farvardin/garvuino/atmega8/amstrad_6128_audio_out.png

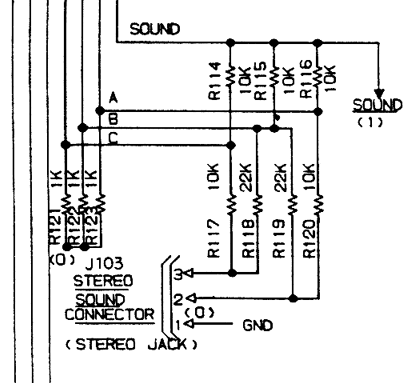
atmega8/amstrad_6128_audio_out.png
