farvardin/garvuino/tools/wave_generator/images/watermelon-duck-outline.png

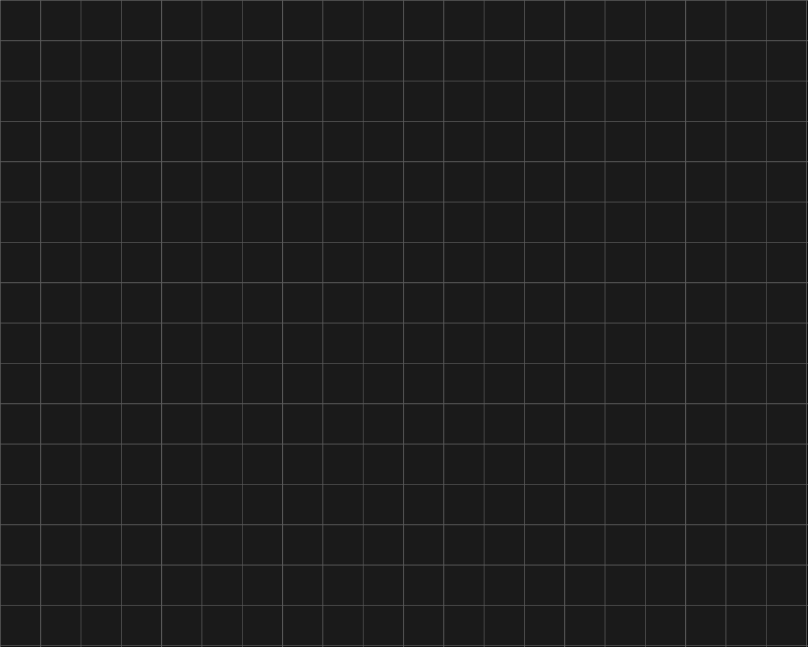
tools/wave_generator/images/watermelon-duck-outline.png
