farvardin/garvuino/arduino_sketches/others/playtune/miditone/garvalf_fugue01.ino

#include <Playtune.h>
// Playtune bytestream for file "garvalf_fugue01.mid" created by MIDITONES V2.00 on Mon Jun 22 09:18:14 2020
// command line: ./miditones -v -i -pt -d -t=4 garvalf_fugue01 
const unsigned char PROGMEM score [] = {
'P','t', 6, 0xE0, 0x00,  4, // (Playtune file header)
0xC0,40, 0x90,64,80, 0,177, 0x80, 0,1, 0x90,69,80, 0,177, 0x80, 0,2, 0x90,72,80, 0,177, 0x80, 0,1, 
0x90,71,80, 0,177, 0x80, 0,2, 0x90,68,80, 0,177, 0x80, 0,1, 0x90,71,80, 0,177, 0x80, 0,2, 0x90,69,80, 
0,177, 0x80, 0,1, 0x90,71,80, 0,178, 0x80, 0,1, 0x90,72,80, 0,177, 0x80, 0,2, 0x90,74,80, 0,177, 
0x80, 0,1, 0x90,76,80, 0,177, 0x80, 0,2, 0x90,74,80, 0,177, 0x80, 0,1, 0x90,69,80, 0,177, 0x80, 0,2, 
0x90,72,80, 0,177, 0x80, 0,1, 0x90,71,80, 1,100, 0x80, 0,2, 0x90,72,80, 0,177, 0x80, 0,1, 0x90,74,80, 
0,177, 0x80, 0,2, 0x90,76,80, 0,177, 0x80, 0,1, 0x90,74,80, 0,177, 0x80, 0,2, 0x90,77,80, 0,177, 
0x80, 0,1, 0x90,76,80, 0,178, 0x80, 0,1, 0x90,74,80, 1,100, 0x80, 0,1, 0x90,72,80, 0,177, 0x80, 0,2, 
0x90,74,80, 0,177, 0x80, 0,1, 0x90,76,80, 0,177, 0x80, 0,2, 0x90,74,80, 0,177, 0x80, 0,1, 0x90,72,80, 
0,178, 0x80, 0,1, 0x90,71,80, 0,177, 0x80, 0,2, 0x90,69,80, 1,99, 0x80, 0,2, 0x90,72,80, 0,177, 
0x80, 0,1, 0x90,76,80, 0,177, 0x80, 0,2, 0x90,79,80, 0,177, 0x80, 0,1, 0x90,77,80, 0,178, 0x80, 0,1, 
0x90,76,80, 0,177, 0x80, 0,2, 0x90,74,80, 0,177, 0x80, 0,1, 0x90,72,80, 1,100, 0x80, 0,1, 0xC0,41, 
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
Playtune pt; 
 void setup() {
  pt.tune_initchan (10); 
  pt.tune_initchan (11);
  pt.tune_initchan (12);
}

 void loop () {
  pt.tune_playscore((byte *) score);  /* start playing */
  while (pt.tune_playing) ;   /* wait here until playing stops */
}
