farvardin/garvuino/arduino_sketches/mozzi/mozzi_MIDI_portamento_POT/mozzi_MIDI_portamento_POT.ino

/* 
 *  Mozzi + Midi + Control portamento strength with Pot 1 in A0  
 * 
 *  version for Garvuino https://github.com/farvardin/garvuino
 *  Works with Arduino IDE 1.8.3
 *  
 *  (it might crackle and produce hiss and noise if the Pot value is too high)
 */


/*  Example of a sound being triggered by MIDI input, with portamento.
  
    Demonstrates playing notes with Mozzi in response to MIDI input.
    Also demonstrates Portamento(), a traditional portamento with a 
    duration which can be set.
  
    Uses Arduino MIDI library v4.2 
    (https://github.com/FortySevenEffects/arduino_midi_library/releases/tag/4.2)
    
    Circuit: 
      MIDI input circuit as per http://arduino.cc/en/Tutorial/Midi
      (midi has to be disconnected from rx for sketch to upload)
      Audio output on digital pin 9 on a Uno or similar.
      
    Mozzi help/discussion/announcements:
    https://groups.google.com/forum/#!forum/mozzi-users
  
    Tim Barrass 2013, CC by-nc-sa.
*/

#include <MIDI.h>
#include <MozziGuts.h>
#include <Oscil.h> // oscillator template
#include <Line.h> // for envelope
#include <tables/sin2048_int8.h> // sine table for oscillator
#include <mozzi_midi.h>
#include <ADSR.h>
#include <mozzi_fixmath.h>
#include <Portamento.h>

MIDI_CREATE_DEFAULT_INSTANCE();

// use #define for CONTROL_RATE, not a constant
#define CONTROL_RATE 128 // powers of 2 please

// audio sinewave oscillator
Oscil <SIN2048_NUM_CELLS, AUDIO_RATE> aSin(SIN2048_DATA);

// envelope generator
ADSR <CONTROL_RATE, AUDIO_RATE> envelope;

Portamento <CONTROL_RATE>aPortamento;

#define LED 8 

const int KNOB_PIN_1 = 0; // set the input for the knob to analog pin 0
int knob_value_1 = 5;

void HandleNoteOn(byte channel, byte note, byte velocity) {
  aPortamento.start(note);
  envelope.noteOn();
  digitalWrite(LED,HIGH);
}



void HandleNoteOff(byte channel, byte note, byte velocity) { 
  envelope.noteOff();
  digitalWrite(LED,LOW);
}



void setup() {
  pinMode(LED, OUTPUT);

  // Initiate MIDI communications, listen to all channels
  MIDI.begin(MIDI_CHANNEL_OMNI);    

  // Connect the HandleNoteOn function to the library, so it is called upon reception of a NoteOn.
  MIDI.setHandleNoteOn(HandleNoteOn);  // Put only the name of the function
  MIDI.setHandleNoteOff(HandleNoteOff);  // Put only the name of the function

  envelope.setADLevels(255,64);
  envelope.setTimes(50,200,10000,300); // 10000 is so the note will sustain 10 seconds unless a noteOff comes

  //aPortamento.setTime(300u);

  startMozzi(CONTROL_RATE); 
  //Serial.begin(115200);
}


void updateControl(){
  MIDI.read();
  envelope.update();
  int knob_value_1 = analogRead(KNOB_PIN_1); // value is 0-1023
  int knob_value_remap = map(knob_value_1,0,1023, 1, 500);
  //int knob_value_constrained constrain(knob_value_1,10,255);
  aPortamento.setTime(knob_value_remap);
  aSin.setFreq_Q16n16(aPortamento.next());
 //Serial.print("input = ");
 // Serial.println((int)input);
 //  Serial.print("knob = ");
  //Serial.println((int)KNOB_PIN_1);
}


int updateAudio(){
  return (int) (envelope.next() * aSin.next())>>8;
}


void loop() {
  audioHook(); // required here
} 
