farvardin/garvuino/arduino_sketches/others/the_synth_midi/WTellOver/SongDat3.h

//*************************************************
//10740 bytes 0 based.
//Adapted from Tandy Color Computer by Rich Cook in March 2016
//  THE WILLIAM TELLOVERTURE
//  BY GARRY AND LINDA HOWARD
//  8931 COMANCHE ROAD LONGMONT, COLORADO 80501
//  COPYRIGHT 1982
//
//Modified 255 for no note change
//*************************************************
//
// time (0-127), note1, note2, note3, note4
//
#include <avr/pgmspace.h>
const PROGMEM char mynotes[] = {
32, 67, 59, 50, 43, 
8, 69, 255, 255, 255, 
8, 62, 255, 255, 255, 
8, 67, 255, 255, 255, 
8, 71, 255, 255, 255, 
8, 62, 255, 255, 255, 
32, 67, 255, 255, 255, 
8, 69, 255, 255, 255, 
8, 62, 255, 255, 255, 
8, 67, 255, 255, 255, 
8, 71, 255, 255, 255, 
8, 62, 255, 255, 255, 
32, 67, 255, 255, 255, 
8, 71, 255, 255, 255, 
8, 76, 255, 255, 255, 
8, 74, 255, 255, 255, 
8, 62, 255, 255, 255, 
8, 71, 255, 255, 255, 
68, 69, 50, 54, 57, 
2, 68, 255, 255, 255, 
2, 69, 255, 255, 255, 
24, 74, 255, 255, 255, 
48, 0, 0, 0, 0, 
32, 67, 59, 55, 50, 
8, 69, 255, 255, 255, 
8, 62, 255, 255, 255, 
8, 67, 255, 255, 255, 
8, 71, 255, 255, 255, 
8, 62, 255, 255, 255, 
32, 67, 255, 255, 255, 
8, 69, 255, 255, 255, 
8, 62, 255, 255, 255, 
8, 67, 255, 255, 255, 
8, 71, 255, 255, 255, 
8, 62, 255, 255, 255, 
32, 67, 255, 255, 255, 
8, 71, 255, 255, 255, 
8, 76, 255, 255, 255, 
8, 74, 255, 255, 255, 
8, 62, 255, 255, 255, 
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

};
