farvardin/garvuino/arduino_sketches/others/playtune/playtune_nano/bach01.h

// Playtune bytestream for file "bach_bwv798.mid" created by MIDITONES V1.1 on Sun Feb 27 12:45:00 2011
const byte PROGMEM score [] = {
  // Sinfonia No.12 in A major BWV.798 J.S.Bach
  // Conductor Track
  7,208, 0x90,0x45, 0x91,0x39, 1,77, 0x80, 0x81, 0x90,0x44, 0,166, 0x80, 0x90,0x45, 0,166, 0x80, 0x90,0x47, 
  0x91,0x38, 1,77, 0x80, 0x81, 0x90,0x45, 0,166, 0x80, 0x90,0x44, 0,166, 0x80, 0x90,0x45, 0x91,0x36, 1,77, 
  0x81, 1,77, 0x91,0x31, 0,166, 0x80, 0x90,0x47, 0,166, 0x80, 0x81, 0x90,0x44, 0,166, 0x80, 0x90,0x45, 
  0,166, 0x80, 0x90,0x47, 0x91,0x32, 0,166, 0x80, 0x90,0x40, 0,166, 0x80, 0x81, 0x90,0x49, 0,166, 0x80, 
  0x90,0x40, 0,166, 0x80, 0x90,0x4A, 0x91,0x34, 0,166, 0x80, 0x90,0x40, 0,166, 0x80, 0x81, 0x90,0x4C, 1,77, 
  0x80, 0x90,0x49, 0x91,0x2D, 0,166, 0x80, 0x90,0x47, 0,166, 0x80, 0x81, 0x90,0x45, 0x91,0x39, 0,166, 0x80, 
  0x90,0x47, 0,166, 0x80, 0x81, 0x90,0x49, 0x91,0x38, 0,166, 0x80, 0x90,0x4B, 0,166, 0x80, 0x81, 0x90,0x4C, 
  0x91,0x36, 0,166, 0x80, 0x90,0x4E, 0,166, 0x80, 0x81, 0x90,0x50, 0x91,0x34, 0x92,0x40, 0,166, 0x80, 0x90,0x51, 
  0,166, 0x80, 0x81, 0x82, 0x90,0x53, 0x91,0x3F, 0,166, 0x81, 0x91,0x40, 0,166, 0x81, 0x91,0x3F, 0x92,0x42, 
  0,166, 0x80, 0x90,0x51, 0,166, 0x80, 0x81, 0x82, 0x90,0x50, 0x91,0x40, 0,166, 0x80, 0x81, 0x90,0x4E, 0x91,0x3F, 
  0,166, 0x80, 0x81, 0x90,0x4C, 0x91,0x3D, 0x92,0x40, 0,166, 0x80, 0x90,0x4B, 0,166, 0x80, 0x81, 0x90,0x49, 
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
  0x91,0x3F, 0x92,0x3B, 1,77, 0x80, 0x81, 0x82, 0x90,0x50, 0x91,0x34, 0x92,0x40, 0,166, 0x80, 0x90,0x51, 0,166, 
  0x80, 0x90,0x53, 0,166, 0x80, 0x90,0x51, 0,166, 0x80, 0x81, 0x82, 0x90,0x50, 0,166, 0x80, 0x90,0x4E, 0x91,0x39, 
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
// This score contains 3203 bytes, and 3 tone generators are used.
