farvardin/garvuino/arduino_sketches/others/vra8-n-mono_7/DigitalSynthVRA8N/filter-table.h

#pragma once

const uint8_t g_filter_lpf_table_0[] PROGMEM = {
  0x18, 0x00, 0x20, 0x87, 0x18, 0x00, 0x20, 0x87, 0x18, 0x00, 0x20, 0x87, 0x18, 0x00, 0x20, 0x87,
  0x18, 0x00, 0x20, 0x87, 0x19, 0x00, 0x55, 0x87, 0x1a, 0x00, 0x8c, 0x87, 0x1c, 0x00, 0xc5, 0x87,
  0x1e, 0x00, 0xff, 0x87, 0x1f, 0x00, 0x3b, 0x88, 0x21, 0x00, 0x78, 0x88, 0x23, 0x00, 0xb8, 0x88,
  0x25, 0x00, 0xf9, 0x88, 0x27, 0x00, 0x3c, 0x89, 0x2a, 0x00, 0x81, 0x89, 0x2c, 0x00, 0xc8, 0x89,
  0x2f, 0x00, 0x11, 0x8a, 0x31, 0x00, 0x5d, 0x8a, 0x34, 0x00, 0xaa, 0x8a, 0x37, 0x00, 0xfa, 0x8a,
  0x3a, 0x00, 0x4c, 0x8b, 0x3e, 0x00, 0xa0, 0x8b, 0x41, 0x00, 0xf7, 0x8b, 0x45, 0x00, 0x50, 0x8c,
  0x49, 0x00, 0xac, 0x8c, 0x4d, 0x00, 0x0b, 0x8d, 0x51, 0x00, 0x6c, 0x8d, 0x56, 0x00, 0xd0, 0x8d,
  0x5b, 0x00, 0x37, 0x8e, 0x60, 0x00, 0xa1, 0x8e, 0x65, 0x00, 0x0e, 0x8f, 0x6b, 0x00, 0x7e, 0x8f,
  0x71, 0x00, 0xf1, 0x8f, 0x78, 0x00, 0x68, 0x90, 0x7e, 0x00, 0xe2, 0x90, 0x85, 0x00, 0x5f, 0x91,
  0x8d, 0x00, 0xe1, 0x91, 0x95, 0x00, 0x65, 0x92, 0x9d, 0x00, 0xee, 0x92, 0xa6, 0x00, 0x7a, 0x93,
  0xaf, 0x00, 0x0b, 0x94, 0xb8, 0x00, 0x9f, 0x94, 0xc3, 0x00, 0x38, 0x95, 0xcd, 0x00, 0xd5, 0x95,
  0xd9, 0x00, 0x76, 0x96, 0xe4, 0x00, 0x1d, 0x97, 0xf1, 0x00, 0xc7, 0x97, 0xfe, 0x00, 0x77, 0x98,
  0x0c, 0x01, 0x2b, 0x99, 0x1a, 0x01, 0xe5, 0x99, 0x2a, 0x01, 0xa3, 0x9a, 0x3a, 0x01, 0x67, 0x9b,
  0x4b, 0x01, 0x30, 0x9c, 0x5c, 0x01, 0xff, 0x9c, 0x6f, 0x01, 0xd4, 0x9d, 0x83, 0x01, 0xaf, 0x9e,
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
};

const uint8_t* g_filter_lpf_tables[] = {
  g_filter_lpf_table_0 , g_filter_lpf_table_1 , g_filter_lpf_table_2 , g_filter_lpf_table_3 ,
  g_filter_lpf_table_4 , g_filter_lpf_table_5 , g_filter_lpf_table_6 , g_filter_lpf_table_7 ,
  g_filter_lpf_table_7 , };
