farvardin/garvuino/arduino_sketches/others/vra8-n-mono_7/DigitalSynthVRA8N/osc-table.h

#pragma once

const __uint24 g_osc_freq_table[] = {
  0x000893, 0x000915, 0x00099F, 0x000A31, 0x000ACD, 0x000B71,
  0x000C1F, 0x000CD9, 0x000D9B, 0x000E6B, 0x000F47, 0x00102F,
  0x001125, 0x00122B, 0x00133F, 0x001463, 0x00159B, 0x0016E3,
  0x00183F, 0x0019B1, 0x001B37, 0x001CD5, 0x001E8D, 0x00205D,
  0x00224B, 0x002455, 0x00267D, 0x0028C7, 0x002B35, 0x002DC7,
  0x00307F, 0x003361, 0x00366F, 0x0039AB, 0x003D19, 0x0040BB,
  0x004495, 0x0048A9, 0x004CFB, 0x00518F, 0x005669, 0x005B8D,
  0x0060FD, 0x0066C3, 0x006CDF, 0x007357, 0x007A33, 0x008177,
  0x00892B, 0x009153, 0x0099F7, 0x00A31F, 0x00ACD1, 0x00B719,
  0x00C1FB, 0x00CD85, 0x00D9BD, 0x00E6AF, 0x00F467, 0x0102EF,
  0x011255, 0x0122A5, 0x0133EF, 0x01463D, 0x0159A3, 0x016E31,
  0x0183F7, 0x019B09, 0x01B37B, 0x01CD5F, 0x01E8CF, 0x0205DF,
  0x0224AB, 0x02454B, 0x0267DD, 0x028C7B, 0x02B347, 0x02DC63,
  0x0307EF, 0x033613, 0x0366F5, 0x039ABF, 0x03D19D, 0x040BBF,
  0x044957, 0x048A97, 0x04CFB9, 0x0518F7, 0x05668F, 0x05B8C5,
  0x060FDF, 0x066C25, 0x06CDEB, 0x07357F, 0x07A33B, 0x08177F,
  0x0892AD, 0x09152D, 0x099F71, 0x0A31ED, 0x0ACD1D, 0x0B7189,
  0x0C1FBD, 0x0CD84B, 0x0D9BD5, 0x0E6AFD, 0x0F4677, 0x102EFF,
  0x112559, 0x122A5B, 0x133EE1, 0x1463D9, 0x159A3B, 0x16E313,
  0x183F79, 0x19B097, 0x1B37A9, 0x1CD5F9, 0x1E8CEF, 0x205DFD,
  0x224AB3, };

const int8_t g_osc_tune_table[] = {
    -15,   -14,   -14,   -14,   -14,   -14,   -14,   -14,
    -14,   -14,   -13,   -13,   -13,   -13,   -13,   -13,
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
  0xC7, 0xC8, 0xCA, 0xCB, 0xCD, 0xCE, 0xD0, 0xD1, 0xD3, 0xD5, 0xD6, 0xD8, 0xDA, 0xDC, 0xDE, 0xDF,
  0xE1, 0xE3, 0xE5, 0xE7, 0xE9, 0xEB, 0xED, 0xEF, 0xF1, 0xF3, 0xF5, 0xF7, 0xF9, 0xFB, 0xFD, 0xFF,
  0x00,
};

const uint8_t g_osc_sin_wave_table_h1[] PROGMEM = {
  0x01, 0x04, 0x07, 0x0A, 0x0E, 0x11, 0x14, 0x17, 0x1A, 0x1D, 0x20, 0x23, 0x26, 0x29, 0x2C, 0x2F,
  0x32, 0x35, 0x38, 0x3A, 0x3D, 0x40, 0x43, 0x45, 0x48, 0x4A, 0x4D, 0x4F, 0x52, 0x54, 0x57, 0x59,
  0x5B, 0x5D, 0x5F, 0x61, 0x63, 0x65, 0x67, 0x69, 0x6B, 0x6C, 0x6E, 0x70, 0x71, 0x73, 0x74, 0x75,
  0x76, 0x77, 0x79, 0x7A, 0x7A, 0x7B, 0x7C, 0x7D, 0x7D, 0x7E, 0x7E, 0x7F, 0x7F, 0x7F, 0x7F, 0x7F,
  0x7F, 0x7F, 0x7F, 0x7F, 0x7F, 0x7E, 0x7E, 0x7D, 0x7D, 0x7C, 0x7B, 0x7A, 0x7A, 0x79, 0x77, 0x76,
  0x75, 0x74, 0x73, 0x71, 0x70, 0x6E, 0x6C, 0x6B, 0x69, 0x67, 0x65, 0x63, 0x61, 0x5F, 0x5D, 0x5B,
  0x59, 0x57, 0x54, 0x52, 0x4F, 0x4D, 0x4A, 0x48, 0x45, 0x43, 0x40, 0x3D, 0x3A, 0x38, 0x35, 0x32,
  0x2F, 0x2C, 0x29, 0x26, 0x23, 0x20, 0x1D, 0x1A, 0x17, 0x14, 0x11, 0x0E, 0x0A, 0x07, 0x04, 0x01,
  0xFE, 0xFB, 0xF8, 0xF5, 0xF1, 0xEE, 0xEB, 0xE8, 0xE5, 0xE2, 0xDF, 0xDC, 0xD9, 0xD6, 0xD3, 0xD0,
  0xCD, 0xCA, 0xC7, 0xC5, 0xC2, 0xBF, 0xBC, 0xBA, 0xB7, 0xB5, 0xB2, 0xB0, 0xAD, 0xAB, 0xA8, 0xA6,
  0xA4, 0xA2, 0xA0, 0x9E, 0x9C, 0x9A, 0x98, 0x96, 0x94, 0x93, 0x91, 0x8F, 0x8E, 0x8C, 0x8B, 0x8A,
  0x89, 0x88, 0x86, 0x85, 0x85, 0x84, 0x83, 0x82, 0x82, 0x81, 0x81, 0x80, 0x80, 0x80, 0x80, 0x80,
  0x80, 0x80, 0x80, 0x80, 0x80, 0x81, 0x81, 0x82, 0x82, 0x83, 0x84, 0x85, 0x85, 0x86, 0x88, 0x89,
  0x8A, 0x8B, 0x8C, 0x8E, 0x8F, 0x91, 0x93, 0x94, 0x96, 0x98, 0x9A, 0x9C, 0x9E, 0xA0, 0xA2, 0xA4,
  0xA6, 0xA8, 0xAB, 0xAD, 0xB0, 0xB2, 0xB5, 0xB7, 0xBA, 0xBC, 0xBF, 0xC2, 0xC5, 0xC7, 0xCA, 0xCD,
  0xD0, 0xD3, 0xD6, 0xD9, 0xDC, 0xDF, 0xE2, 0xE5, 0xE8, 0xEB, 0xEE, 0xF1, 0xF5, 0xF8, 0xFB, 0xFE,
  0x01,
};

const uint8_t* g_osc_saw_wave_tables[] = {
  g_osc_saw_wave_table_h127, g_osc_saw_wave_table_h127, g_osc_saw_wave_table_h127,
  g_osc_saw_wave_table_h127, g_osc_saw_wave_table_h127, g_osc_saw_wave_table_h127,
  g_osc_saw_wave_table_h127, g_osc_saw_wave_table_h127, g_osc_saw_wave_table_h127,
  g_osc_saw_wave_table_h127, g_osc_saw_wave_table_h127, g_osc_saw_wave_table_h127,
  g_osc_saw_wave_table_h127, g_osc_saw_wave_table_h127, g_osc_saw_wave_table_h127,
  g_osc_saw_wave_table_h127, g_osc_saw_wave_table_h127, g_osc_saw_wave_table_h127,
  g_osc_saw_wave_table_h127, g_osc_saw_wave_table_h127, g_osc_saw_wave_table_h127,
  g_osc_saw_wave_table_h127, g_osc_saw_wave_table_h127, g_osc_saw_wave_table_h127,
  g_osc_saw_wave_table_h127, g_osc_saw_wave_table_h127, g_osc_saw_wave_table_h127,
  g_osc_saw_wave_table_h127, g_osc_saw_wave_table_h127, g_osc_saw_wave_table_h127,
  g_osc_saw_wave_table_h127, g_osc_saw_wave_table_h127, g_osc_saw_wave_table_h127,
  g_osc_saw_wave_table_h127, g_osc_saw_wave_table_h127, g_osc_saw_wave_table_h127,
  g_osc_saw_wave_table_h127, g_osc_saw_wave_table_h127, g_osc_saw_wave_table_h127,
  g_osc_saw_wave_table_h127, g_osc_saw_wave_table_h127, g_osc_saw_wave_table_h127,
  g_osc_saw_wave_table_h127, g_osc_saw_wave_table_h127, g_osc_saw_wave_table_h127,
  g_osc_saw_wave_table_h127, g_osc_saw_wave_table_h112, g_osc_saw_wave_table_h112,
  g_osc_saw_wave_table_h112, g_osc_saw_wave_table_h94 , g_osc_saw_wave_table_h94 ,
  g_osc_saw_wave_table_h94 , g_osc_saw_wave_table_h79 , g_osc_saw_wave_table_h79 ,
  g_osc_saw_wave_table_h79 , g_osc_saw_wave_table_h67 , g_osc_saw_wave_table_h67 ,
  g_osc_saw_wave_table_h67 , g_osc_saw_wave_table_h56 , g_osc_saw_wave_table_h56 ,
  g_osc_saw_wave_table_h56 , g_osc_saw_wave_table_h47 , g_osc_saw_wave_table_h47 ,
  g_osc_saw_wave_table_h47 , g_osc_saw_wave_table_h39 , g_osc_saw_wave_table_h39 ,
  g_osc_saw_wave_table_h39 , g_osc_saw_wave_table_h33 , g_osc_saw_wave_table_h33 ,
  g_osc_saw_wave_table_h33 , g_osc_saw_wave_table_h28 , g_osc_saw_wave_table_h28 ,
  g_osc_saw_wave_table_h28 , g_osc_saw_wave_table_h23 , g_osc_saw_wave_table_h23 ,
  g_osc_saw_wave_table_h23 , g_osc_saw_wave_table_h19 , g_osc_saw_wave_table_h19 ,
  g_osc_saw_wave_table_h19 , g_osc_saw_wave_table_h16 , g_osc_saw_wave_table_h16 ,
  g_osc_saw_wave_table_h16 , g_osc_saw_wave_table_h14 , g_osc_saw_wave_table_h14 ,
  g_osc_saw_wave_table_h14 , g_osc_saw_wave_table_h11 , g_osc_saw_wave_table_h11 ,
  g_osc_saw_wave_table_h11 , g_osc_saw_wave_table_h9  , g_osc_saw_wave_table_h9  ,
  g_osc_saw_wave_table_h9  , g_osc_saw_wave_table_h8  , g_osc_saw_wave_table_h8  ,
  g_osc_saw_wave_table_h8  , g_osc_saw_wave_table_h7  , g_osc_saw_wave_table_h7  ,
  g_osc_saw_wave_table_h7  , g_osc_saw_wave_table_h5  , g_osc_saw_wave_table_h5  ,
  g_osc_saw_wave_table_h5  , g_osc_saw_wave_table_h4  , g_osc_saw_wave_table_h4  ,
  g_osc_saw_wave_table_h4  , g_osc_saw_wave_table_h4  , g_osc_saw_wave_table_h4  ,
  g_osc_saw_wave_table_h4  , g_osc_saw_wave_table_h3  , g_osc_saw_wave_table_h3  ,
  g_osc_saw_wave_table_h3  , g_osc_saw_wave_table_h2  , g_osc_saw_wave_table_h2  ,
  g_osc_saw_wave_table_h2  , g_osc_saw_wave_table_h2  , g_osc_saw_wave_table_h2  ,
  g_osc_saw_wave_table_h2  , g_osc_saw_wave_table_h2  , g_osc_saw_wave_table_h2  ,
  g_osc_saw_wave_table_h2  , g_osc_saw_wave_table_h1  , g_osc_saw_wave_table_h1  ,
  g_osc_saw_wave_table_h1  , };

const uint8_t* g_osc_sq_wave_tables[] = {
  g_osc_sq_wave_table_h127, g_osc_sq_wave_table_h127, g_osc_sq_wave_table_h127,
  g_osc_sq_wave_table_h127, g_osc_sq_wave_table_h127, g_osc_sq_wave_table_h127,
  g_osc_sq_wave_table_h127, g_osc_sq_wave_table_h127, g_osc_sq_wave_table_h127,
  g_osc_sq_wave_table_h127, g_osc_sq_wave_table_h127, g_osc_sq_wave_table_h127,
  g_osc_sq_wave_table_h127, g_osc_sq_wave_table_h127, g_osc_sq_wave_table_h127,
  g_osc_sq_wave_table_h127, g_osc_sq_wave_table_h127, g_osc_sq_wave_table_h127,
  g_osc_sq_wave_table_h127, g_osc_sq_wave_table_h127, g_osc_sq_wave_table_h127,
  g_osc_sq_wave_table_h127, g_osc_sq_wave_table_h127, g_osc_sq_wave_table_h127,
  g_osc_sq_wave_table_h127, g_osc_sq_wave_table_h127, g_osc_sq_wave_table_h127,
  g_osc_sq_wave_table_h127, g_osc_sq_wave_table_h127, g_osc_sq_wave_table_h127,
  g_osc_sq_wave_table_h127, g_osc_sq_wave_table_h127, g_osc_sq_wave_table_h127,
  g_osc_sq_wave_table_h127, g_osc_sq_wave_table_h127, g_osc_sq_wave_table_h127,
  g_osc_sq_wave_table_h127, g_osc_sq_wave_table_h127, g_osc_sq_wave_table_h127,
  g_osc_sq_wave_table_h127, g_osc_sq_wave_table_h127, g_osc_sq_wave_table_h127,
  g_osc_sq_wave_table_h127, g_osc_sq_wave_table_h127, g_osc_sq_wave_table_h127,
  g_osc_sq_wave_table_h127, g_osc_sq_wave_table_h112, g_osc_sq_wave_table_h112,
  g_osc_sq_wave_table_h112, g_osc_sq_wave_table_h94 , g_osc_sq_wave_table_h94 ,
  g_osc_sq_wave_table_h94 , g_osc_sq_wave_table_h79 , g_osc_sq_wave_table_h79 ,
  g_osc_sq_wave_table_h79 , g_osc_sq_wave_table_h67 , g_osc_sq_wave_table_h67 ,
  g_osc_sq_wave_table_h67 , g_osc_sq_wave_table_h56 , g_osc_sq_wave_table_h56 ,
  g_osc_sq_wave_table_h56 , g_osc_sq_wave_table_h47 , g_osc_sq_wave_table_h47 ,
  g_osc_sq_wave_table_h47 , g_osc_sq_wave_table_h39 , g_osc_sq_wave_table_h39 ,
  g_osc_sq_wave_table_h39 , g_osc_sq_wave_table_h33 , g_osc_sq_wave_table_h33 ,
  g_osc_sq_wave_table_h33 , g_osc_sq_wave_table_h28 , g_osc_sq_wave_table_h28 ,
  g_osc_sq_wave_table_h28 , g_osc_sq_wave_table_h23 , g_osc_sq_wave_table_h23 ,
  g_osc_sq_wave_table_h23 , g_osc_sq_wave_table_h19 , g_osc_sq_wave_table_h19 ,
  g_osc_sq_wave_table_h19 , g_osc_sq_wave_table_h16 , g_osc_sq_wave_table_h16 ,
  g_osc_sq_wave_table_h16 , g_osc_sq_wave_table_h14 , g_osc_sq_wave_table_h14 ,
  g_osc_sq_wave_table_h14 , g_osc_sq_wave_table_h11 , g_osc_sq_wave_table_h11 ,
  g_osc_sq_wave_table_h11 , g_osc_sq_wave_table_h9  , g_osc_sq_wave_table_h9  ,
  g_osc_sq_wave_table_h9  , g_osc_sq_wave_table_h8  , g_osc_sq_wave_table_h8  ,
  g_osc_sq_wave_table_h8  , g_osc_sq_wave_table_h7  , g_osc_sq_wave_table_h7  ,
  g_osc_sq_wave_table_h7  , g_osc_sq_wave_table_h5  , g_osc_sq_wave_table_h5  ,
  g_osc_sq_wave_table_h5  , g_osc_sq_wave_table_h4  , g_osc_sq_wave_table_h4  ,
  g_osc_sq_wave_table_h4  , g_osc_sq_wave_table_h4  , g_osc_sq_wave_table_h4  ,
  g_osc_sq_wave_table_h4  , g_osc_sq_wave_table_h3  , g_osc_sq_wave_table_h3  ,
  g_osc_sq_wave_table_h3  , g_osc_sq_wave_table_h2  , g_osc_sq_wave_table_h2  ,
  g_osc_sq_wave_table_h2  , g_osc_sq_wave_table_h2  , g_osc_sq_wave_table_h2  ,
  g_osc_sq_wave_table_h2  , g_osc_sq_wave_table_h2  , g_osc_sq_wave_table_h2  ,
  g_osc_sq_wave_table_h2  , g_osc_sq_wave_table_h1  , g_osc_sq_wave_table_h1  ,
  g_osc_sq_wave_table_h1  , };
