farvardin/garvuino/arduino_sketches/sid/sid_player/temp_dmp.h

const int sidLength = 25499;  //number of bytes in array
const char sidData[] PROGMEM = {
	 0,0,0,0,0,0,0,0,0,0,0,0,0,0,0,0,0,0,0,
    0,0,0,0,0,15,113,2,0,0,0,15,0,0,0,0,0,0,0,0,
    113,2,0,0,0,15,0,0,0,0,15,113,2,0,0,0,15,0,0,0,
    0,0,0,0,0,113,2,0,0,0,15,0,0,0,0,15,113,1,0,0,
    9,18,-63,113,2,15,0,0,0,0,113,2,0,0,9,16,0,0,0,5,
    15,-60,9,-11,4,97,18,-63,113,2,30,0,0,0,0,56,1,0,0,33,
    16,0,0,82,37,31,-59,9,-11,4,97,18,-63,113,2,45,0,0,0,0,
    56,1,0,0,49,16,0,0,82,37,31,-59,9,-11,4,97,18,-63,113,2,
    60,0,0,0,0,57,1,0,0,49,16,0,0,82,37,31,-59,9,-11,4,
    97,18,-63,113,2,75,0,0,0,0,57,1,0,0,49,16,0,0,82,37,
    31,-59,9,-11,4,97,18,-63,113,2,90,0,0,0,0,57,1,0,0,49,
    16,0,0,82,37,31,-59,9,-11,4,97,18,-63,113,2,105,0,0,0,0,
    57,1,0,0,49,16,0,0,82,37,31,-59,9,-11,4,97,18,-63,113,2,
    120,0,0,0,0,57,1,0,0,49,16,0,0,82,37,31,-59,9,-11,4,
    97,18,-63,113,2,-121,0,0,0,0,57,1,0,0,49,16,0,0,82,37,
    31,-59,9,-11,4,97,18,-63,113,2,-106,0,0,0,0,57,1,0,0,49,
    16,0,0,82,37,31,-59,9,-11,4,97,18,-63,113,2,-106,0,0,0,0,
    57,1,0,0,49,16,0,0,82,37,31,-59,9,-11,4,97,18,-63,17,-44,
    -120,0,0,0,0,57,1,0,0,49,16,0,0,82,37,31,-59,9,-11,4,
    97,18,-63,8,1,122,0,0,0,0,57,1,0,0,49,16,0,0,82,37,
    31,-59,9,-11,4,97,18,-63,-64,4,108,0,0,0,0,57,1,0,0,49,
    16,0,0,82,37,31,-59,9,-11,4,97,18,-63,7,1,94,0,0,0,0,
    57,1,0,0,49,16,0,0,82,37,31,-59,9,-11,4,97,18,-63,-128,110,
    80,0,0,0,0,57,1,0,0,49,16,0,0,82,37,31,-59,9,-11,4,
    97,18,-63,-128,110,66,0,0,0,0,57,1,0,0,49,16,0,0,82,37,
    31,-59,9,-11,4,97,18,-63,-128,110,52,0,0,0,0,57,1,0,0,49,
    16,0,0,82,37,31,-59,9,-11,4,97,18,-63,-128,110,38,0,0,0,0,
    57,1,0,0,49,16,0,0,82,37,31,-59,9,-11,4,97,18,-63,-128,110,
    24,0,0,0,0,57,1,0,0,49,16,0,0,82,37,31,-59,9,-11,4,
    97,18,-63,-128,110,10,0,0,0,0,57,1,0,0,49,16,0,0,82,37,
    31,-59,9,-11,4,97,18,-63,-128,110,-4,-1,0,0,0,57,1,0,0,49,
    16,0,0,82,37,31,-59,9,-11,4,97,18,-63,-128,110,-18,-1,0,0,0,
    57,1,0,0,49,16,0,0,82,37,31,-59,9,-11,4,97,18,-63,-128,110,
    -32,-1,0,0,0,57,1,0,0,49,16,0,0,82,37,31,-59,9,-11,4,
    97,18,-63,-128,110,-46,-1,0,0,0,57,1,0,0,49,16,0,0,82,37,
    31,-59,9,-11,4,97,18,-63,-128,110,-60,-1,0,0,0,57,1,0,0,49,
    16,0,0,82,37,31,-59,9,-11,4,97,18,-63,-1,110,-74,-1,0,0,0,
    57,1,0,0,49,16,0,0,82,37,31,-59,9,-11,4,97,18,-63,-89,-32,
    -88,-1,0,0,0,57,1,0,0,49,16,0,0,82,37,31,-59,9,-11,4,
    97,18,-63,-113,1,-102,-1,0,0,0,57,1,0,0,49,16,0,0,82,37,
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
};
