farvardin/garvuino/arduino_sketches/beeper/arduino_phaser1/music_data.h

const unsigned char music_data[] PROGMEM ={
0x00,0x8c,0x08,0x00,0x00,0x01,0x00,0x00,0x01,0x12,0x00,0x1a,0xd8,0x9c,0x27,0xa8,
0xfc,0x9c,0x22,0x9d,0xd8,0x9c,0x27,0xa8,0xfc,0x9c,0x47,0x9d,0x70,0x9d,0x8d,0x9d,
0x5e,0x9e,0x1d,0x9e,0xcb,0x9d,0xb0,0x9e,0x43,0x9f,0xbd,0x9f,0x50,0xa0,0xca,0xa0,
0xee,0xa0,0x11,0xa1,0xee,0xa0,0x35,0xa1,0xee,0xa0,0x59,0xa1,0xee,0xa0,0x7d,0xa1,
0xa1,0xa1,0x7d,0xa1,0x2f,0xa2,0xc4,0xa1,0xa1,0xa1,0xe8,0xa1,0x0c,0xa2,0x52,0xa2,
0x34,0xa3,0xe0,0xa2,0x99,0xa2,0x81,0xa3,0x14,0xa4,0x9e,0xa4,0x31,0xa5,0x9c,0xa5,
0xe3,0xa5,0x9c,0xa5,0x3f,0xa6,0x88,0xa6,0x1d,0xa7,0x88,0xa6,0xb2,0xa7,0x9c,0xa5,
0xe3,0xa5,0x9c,0xa5,0x3f,0xa6,0x88,0xa6,0x1d,0xa7,0x88,0xa6,0x4c,0xa8,0xbc,0xa8,
0xc3,0xa8,0xf3,0xa8,0xf3,0xa8,0xf3,0xa8,0xf3,0xa8,0xf3,0xa8,0xf3,0xa8,0x26,0xa9,
0x42,0xa9,0x47,0xa9,0x47,0xa9,0x47,0xa9,0xbd,0x00,0x80,0x80,0x03,0x82,0x03,0x83,
0x03,0x87,0x03,0x8c,0x03,0x8e,0x03,0x8f,0x03,0x93,0x03,0x98,0x03,0x9a,0x03,0x9b,
0x03,0x9f,0x03,0xa4,0x03,0xa6,0x03,0xa7,0x03,0xab,0x03,0x00,0xbd,0x00,0x80,0x89,
0x03,0x82,0x03,0x83,0x03,0x87,0x03,0x8c,0x03,0x8e,0x03,0x8f,0x95,0x03,0x93,0x03,
0x98,0x03,0x9a,0x03,0x9b,0x03,0x9f,0x03,0xa4,0x89,0x03,0xa6,0x03,0xa7,0x03,0xab,
0x03,0x00,0xbd,0x00,0x80,0x88,0x03,0x82,0x03,0x83,0x03,0x87,0x03,0x8c,0x03,0x8e,
0x03,0x8f,0x03,0x93,0x03,0x98,0x94,0x03,0x9a,0x03,0x9b,0x03,0x9f,0x03,0xa4,0x03,
0xa6,0x03,0xa7,0x03,0xab,0x03,0x00,0xbd,0x00,0x80,0x88,0x03,0x82,0x03,0x83,0x03,
0x87,0x03,0x8c,0x03,0x8e,0x03,0x8f,0x03,0x93,0x03,0x98,0x94,0x03,0x9a,0x03,0x9b,
0x77,0x02,0x9f,0x03,0xa4,0x77,0x02,0xa6,0x03,0xa7,0x77,0x02,0xab,0x77,0x02,0x00,
0x8c,0x80,0x76,0x17,0xbe,0x7a,0x02,0xbe,0x7b,0x02,0xbe,0x7c,0x02,0xbe,0x77,0x02,
0xbe,0x77,0x02,0xbe,0x77,0x02,0xbe,0x77,0x02,0xbe,0x77,0x02,0x00,0xbd,0x00,0x9c,
0x80,0x76,0x03,0xbe,0x8c,0x04,0xbe,0x80,0x77,0x03,0xbe,0x80,0x04,0xbe,0x8c,0x76,
0x03,0xbe,0x80,0x76,0x03,0x9d,0x80,0x77,0x03,0xbe,0x8c,0x04,0x9f,0x80,0x76,0x03,
0xbe,0x80,0x04,0x9d,0x8c,0x77,0x03,0x9c,0x80,0x04,0xbe,0x8c,0x76,0x03,0x9a,0x80,
0x76,0x03,0x98,0x80,0x77,0x03,0xbe,0x8c,0x76,0x03,0x00,0xbd,0x00,0x9a,0x88,0x76,
0x03,0xbe,0x88,0x04,0x98,0x94,0x77,0x9a,0x01,0x9b,0x02,0x98,0x88,0x04,0xbe,0x88,
0x76,0x03,0xbe,0x94,0x76,0x03,0xbe,0x88,0x77,0x03,0xbe,0x94,0x04,0xa1,0x89,0x76,
0x01,0x9c,0x02,0x98,0x89,0x02,0xa4,0x02,0xa1,0x95,0x77,0x01,0x9c,0x02,0x98,0x89,
0x02,0xa4,0x02,0xa0,0x88,0x76,0x01,0x9b,0x02,0x98,0x94,0x76,0x01,0xa2,0x02,0xa0,
0x88,0x77,0x01,0x9b,0x02,0x98,0x94,0x77,0x01,0xa2,0x77,0x01,0x00,0xbd,0x00,0x9f,
0x80,0x76,0x03,0xbe,0x8c,0x04,0xbe,0x80,0x77,0x03,0xbe,0x80,0x04,0xbe,0x8c,0x76,
0x03,0xbe,0x80,0x76,0x03,0x9f,0x80,0x77,0xa0,0x01,0xa2,0x02,0xbe,0x8c,0x04,0x9f,
0x80,0x76,0x03,0xbe,0x80,0x04,0x9d,0x8c,0x77,0x03,0x9b,0x80,0x04,0xbe,0x8c,0x76,
0x03,0x9a,0x80,0x76,0x03,0x98,0x80,0x77,0x03,0xbe,0x8c,0x76,0x03,0x00,0xbd,0x00,
0x9a,0x80,0x76,0x03,0xbe,0x8c,0x04,0x98,0x80,0x77,0x9a,0x01,0x9b,0x02,0x98,0x80,
0x04,0xbe,0x8c,0x76,0x03,0xbe,0x80,0x76,0x03,0xbe,0x80,0x77,0x03,0xbe,0x8c,0x04,
0xa1,0x89,0x76,0x01,0x9c,0x02,0x98,0x89,0x02,0xa4,0x02,0xa1,0x95,0x77,0x01,0x9c,
0x02,0x98,0x89,0x02,0xa4,0x02,0xa0,0x88,0x76,0x01,0x9b,0x02,0x98,0x94,0x76,0x01,
0xa2,0x02,0xa0,0x88,0x77,0x01,0x9b,0x02,0x98,0x94,0x77,0x01,0xa2,0x77,0x01,0x00,
0xbd,0x00,0x9f,0x80,0x76,0x9c,0x01,0x9f,0x01,0x9c,0x01,0x9f,0x8c,0x01,0x9c,0x01,
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
};
