farvardin/garvuino/arduino_sketches/others/playtune/miditone/gervbrg4.h

// Playtune bytestream for file "gervbrg4.mid" created by MIDITONES V2.00 on Mon Jun 22 09:14:45 2020
// command line: ./miditones -v -i -pt -d -t=4 gervbrg4 
const unsigned char PROGMEM score [] = {
'P','t', 6, 0xE0, 0x00,  4, // (Playtune file header)
0xC0,57, 0x90,70,92, 0xC1,111, 0x91,67,75, 0xC2,58, 0x92,62,75, 0xC3,60, 0x93,55,75, 1,77, 0x80, 0x81, 0x82, 0x83, 
0,66, 0x90,70,92, 0x91,67,75, 0x92,62,75, 0x93,55,75, 1,78, 0x80, 0x81, 0x82, 0x83, 0,66, 0x90,70,92, 0x91,67,75, 
0x92,62,75, 0x93,55,75, 2,188, 0x80, 0x81, 0x82, 0x83, 0,100, 0x90,69,92, 0x91,60,75, 0x92,65,75, 0x93,53,75, 
2,188, 0x80, 0x81, 0x82, 0x83, 0,100, 0x90,74,92, 0x91,67,75, 0x92,62,75, 0x93,55,75, 1,78, 0x80, 0x81, 0x82, 0x83, 
0,66, 0x90,74,92, 0x91,69,75, 0x92,65,75, 0x93,50,75, 1,78, 0x80, 0x82, 0x83, 0,66, 0x90,73,92, 0x92,64,75, 
0x93,57,75, 0,134, 0x81, 0,66, 0x91,67,75, 0,196, 0x81, 0,4, 0x91,69,75, 1,44, 0x80, 0x82, 0x83, 0,34, 
0x81, 0,66, 0x90,74,92, 0x91,65,75, 0x92,62,75, 0x93,50,75, 2,188, 0x80, 0x81, 0x82, 0x83, 0,100, 0x90,70,92, 
0x91,67,75, 0x92,62,75, 0x93,55,75, 1,78, 0x80, 0x81, 0x82, 0x83, 0,66, 0x90,70,92, 0x91,67,75, 0x92,62,75, 
0x93,55,75, 1,78, 0x80, 0x81, 0x82, 0x83, 0,66, 0x90,70,92, 0x91,67,75, 0x92,62,75, 0x93,55,75, 2,188, 0x80, 
0x81, 0x82, 0x83, 0,100, 0x90,69,92, 0x91,60,75, 0x92,65,75, 0x93,53,75, 2,188, 0x80, 0x81, 0x82, 0x83, 0,100, 0x90,74,92, 
0x91,67,75, 0x92,62,75, 0x93,55,75, 1,78, 0x80, 0x81, 0x82, 0x83, 0,66, 0x90,74,92, 0x91,69,75, 0x92,65,75, 
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
0x81, 0x82, 0x83, 0,66, 0x90,70,92, 0x91,62,75, 0x92,58,75, 0x93,55,75, 1,78, 0x81, 0,66, 0x91,64,75, 1,44, 
0x80, 0x82, 0x83, 0,34, 0x81, 0,66, 0x90,69,92, 0x91,65,75, 0x92,60,75, 0x93,53,75, 2,188, 0x80, 0x81, 0x82, 0x83, 
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

// This score contains 1433 bytes, and 4 tone generators are used.
