farvardin/garvuino/arduino_sketches/others/playtune/playtune_nano/3ravens.h

// Playtune bytestream for file "3ravens.mid" created by MIDITONES V1.6 on Wed Jan  3 17:14:27 2018
// command line: ./miditones 3ravens 
const byte PROGMEM score [] = {
0x90,71, 0x91,59, 1,144, 0x80, 0x81, 0,80, 0x90,52, 0x91,76, 0x92,64, 0x93,55, 1,144, 0x81, 
0x82, 0x83, 0,80, 0x91,78, 0x92,66, 0x93,57, 1,144, 0x81, 0x82, 0x83, 0,80, 0x91,79, 0x92,67, 
0x93,59, 1,144, 0x81, 0x82, 0,80, 0x91,83, 0x92,71, 1,104, 0x80, 0x83, 0,40, 0x81, 0x82, 0,80, 
0x90,57, 0x91,81, 0x92,69, 0x93,61, 1,144, 0x81, 0x82, 0,80, 0x91,79, 0x92,67, 1,104, 0x83, 
0x80, 0,40, 0x81, 0x82, 0,80, 0x90,59, 0x91,78, 0x92,66, 0x93,63, 3,72, 0x81, 0x82, 0x83, 0x80, 
0,120, 0x90,76, 0x91,59, 0x92,55, 2,128, 0x80, 0x82, 0,80, 0x90,78, 0x92,54, 0,235, 0x80, 
0x82, 0,5, 0x90,79, 0x92,52, 1,144, 0x80, 0x82, 0,80, 0x90,81, 0x92,51, 1,104, 0x81, 0,40, 
0x82, 0x80, 0,80, 0x90,67, 0x91,50, 0x92,83, 0x93,71, 1,144, 0x82, 0x83, 0x80, 0,80, 0x90,84, 
0x92,69, 0x93,72, 1,104, 0x81, 0,40, 0x80, 0x83, 0x82, 0,80, 0x90,43, 0x91,83, 0x92,67, 0x93,71, 
1,144, 0x80, 0x81, 0x83, 0x82, 0,80, 0x90,71, 0x91,59, 1,144, 0x80, 0x81, 0,80, 0x90,52, 0x91,76, 
0x92,64, 0x93,55, 1,144, 0x81, 0x82, 0x83, 0,80, 0x91,78, 0x92,66, 0x93,57, 1,144, 0x81, 0x82, 
0x83, 0,80, 0x91,79, 0x92,67, 0x93,59, 1,144, 0x81, 0x82, 0,80, 0x91,76, 0x92,64, 1,104, 
0x80, 0x83, 0,40, 0x81, 0x82, 0,80, 0x90,50, 0x91,78, 0x92,66, 0x93,62, 1,144, 0x81, 0x82, 0x83, 
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
0x81, 0x84, 0x82, 0,80, 0x90,71, 0x91,59, 1,144, 0x80, 0x81, 0,80, 0x90,52, 0x91,76, 0x92,64, 
0x93,55, 1,144, 0x81, 0x82, 0x83, 0,80, 0x91,78, 0x92,66, 0x93,57, 1,144, 0x81, 0x82, 0x83, 0,80, 
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
// This score contains 1634 bytes, and 5 tone generators are used.
