farvardin/garvuino/arduino_sketches/others/playtune/playtune_nano/garvalf_sanctuaire_hibou.h

// Playtune bytestream for file "sanctuaire_hibou.mid" created by MIDITONES V1.6 on Wed Jan  3 17:24:59 2018
// command line: ./miditones sanctuaire_hibou 
const byte PROGMEM score [] = {
0x90,45, 0x91,52, 0x92,64, 0,236, 0x82, 0,13, 0x92,69, 0,236, 0x82, 0,13, 0x92,76, 0,236, 
0x82, 0,13, 0x92,72, 0,198, 0x80, 0x81, 0,37, 0x82, 0,13, 0x90,45, 0x91,69, 0x92,53, 0,236, 
0x81, 0,13, 0x91,74, 0,236, 0x81, 0,13, 0x91,72, 0,236, 0x81, 0,13, 0x91,76, 0,198, 
0x80, 0x82, 0,37, 0x81, 0,13, 0x90,45, 0x91,64, 0x92,52, 0,236, 0x81, 0,13, 0x91,69, 0,236, 
0x81, 0,13, 0x91,76, 0,236, 0x81, 0,13, 0x91,72, 0,198, 0x80, 0x82, 0,37, 0x81, 0,13, 
0x90,45, 0x91,69, 0x92,53, 0,117, 0x81, 0,7, 0x91,74, 0,117, 0x81, 0,7, 0x91,72, 0,117, 
0x81, 0,7, 0x91,71, 0,117, 0x81, 0,7, 0x91,72, 0,117, 0x81, 0,7, 0x91,74, 0,117, 
0x81, 0,7, 0x91,76, 0,198, 0x80, 0x82, 0,37, 0x81, 0,13, 0x90,45, 0x91,64, 0x92,52, 1,217, 
0x81, 0x80, 0x82, 0,26, 0x90,69, 0x91,41, 1,217, 0x80, 0x81, 0,26, 0x90,64, 0x91,45, 0,236, 
0x80, 0,13, 0x90,62, 0,236, 0x80, 0,13, 0x90,60, 1,192, 0x81, 0,25, 0x80, 0,26, 0x90,38, 
0x91,62, 0x92,45, 0x93,52, 3,180, 0x81, 0x80, 0x82, 0x83, 0,51, 0x90,60, 0x91,45, 0x92,53, 1,217, 
0x80, 0,26, 0x90,60, 0,236, 0x80, 0,13, 0x90,59, 0,198, 0x81, 0x82, 0,37, 0x80, 0,13, 
0x90,45, 0x91,76, 0x92,52, 0,236, 0x81, 0x80, 0x82, 0,13, 0x90,69, 0x91,45, 0x92,52, 0,236, 
0x80, 0x81, 0x82, 0,13, 0x90,77, 0x91,45, 0x92,53, 0,236, 0x80, 0,13, 0x90,71, 0,223, 0x81, 
0x82, 0,12, 0x80, 0,13, 0x90,45, 0x91,72, 0x92,52, 0,236, 0x81, 0,13, 0x91,74, 0,236, 
0x81, 0,13, 0x91,76, 0,236, 0x81, 0,13, 0x91,69, 0,198, 0x80, 0x82, 0,37, 0x81, 0,13, 
0x90,45, 0x91,64, 0x92,52, 0,236, 0x81, 0x80, 0x82, 0,13, 0x90,57, 0x91,45, 0x92,52, 0,236, 
0x80, 0x81, 0x82, 0,13, 0x90,65, 0x91,45, 0x92,53, 0,236, 0x80, 0,13, 0x90,59, 0,223, 0x81, 
0x82, 0,12, 0x80, 0,13, 0x90,45, 0x91,60, 0x92,52, 0,117, 0x81, 0,7, 0x91,59, 0,117, 
0x81, 0,7, 0x91,60, 0,117, 0x81, 0,7, 0x91,62, 0,117, 0x81, 0,7, 0x91,64, 0,236, 
0x81, 0,13, 0x91,57, 0,198, 0x80, 0x82, 0,37, 0x81, 0,13, 0x90,45, 0x91,65, 0x92,52, 0,236, 
0x81, 0,13, 0x91,64, 0,236, 0x81, 0,13, 0x91,60, 1,192, 0x80, 0x82, 0,25, 0x81, 0,26, 
0x90,45, 0x91,65, 0x92,53, 0,236, 0x81, 0,13, 0x91,64, 0,236, 0x81, 0,13, 0x91,62, 0,117, 
0x81, 0,7, 0x91,64, 0,117, 0x81, 0,7, 0x91,65, 0,198, 0x80, 0x82, 0,37, 0x81, 0,13, 
0x90,45, 0x91,59, 0x92,52, 1,217, 0x81, 0,26, 0x91,62, 0,236, 0x81, 0,13, 0x91,60, 0,198, 
0x80, 0x82, 0,37, 0x81, 0,13, 0x90,45, 0x91,65, 0x92,53, 0,117, 0x81, 0,7, 0x91,64, 0,117, 
0x81, 0,7, 0x91,62, 0,117, 0x81, 0,7, 0x91,60, 0,117, 0x81, 0,7, 0x91,69, 0,117, 
0x81, 0,7, 0x91,64, 0,117, 0x81, 0,7, 0x91,57, 0,198, 0x80, 0x82, 0,37, 0x81, 0,13, 
0x90,45, 0x91,69, 0x92,52, 1,217, 0x81, 0x80, 0x82, 0,26, 0x90,57, 0x91,41, 1,217, 0x80, 0x81, 
0,26, 0x90,64, 0x91,45, 1,217, 0x80, 0,26, 0x90,64, 0,236, 0x80, 0,13, 0x90,64, 0,198, 
0x81, 0,37, 0x80, 0,13, 0x90,38, 0x91,57, 0x92,45, 0x93,52, 3,180, 0x81, 0x80, 0x82, 0x83, 0,51, 
0x90,60, 0x91,45, 0x92,53, 1,217, 0x80, 0,26, 0x90,62, 1,192, 0x81, 0x82, 0,25, 0x80, 0,26, 
0x90,45, 0x91,64, 0x92,52, 1,217, 0x81, 0x80, 0x82, 0,26, 0x90,57, 0x91,41, 1,217, 0x80, 0x81, 
0,26, 0x90,69, 0x91,45, 1,217, 0x80, 0,26, 0x90,69, 0,236, 0x80, 0,13, 0x90,69, 0,198, 
0x81, 0,37, 0x80, 0,13, 0x90,38, 0x91,64, 0x92,45, 0x93,52, 3,180, 0x81, 0x80, 0x82, 0x83, 0,51, 
0x90,65, 0x91,45, 0x92,53, 1,217, 0x80, 0,26, 0x90,67, 1,192, 0x81, 0x82, 0,25, 0x80, 0,26, 
0x90,48, 0x91,67, 0x92,55, 0,236, 0x81, 0,13, 0x91,72, 0,236, 0x81, 0,13, 0x91,79, 0,236, 
0x81, 0,13, 0x91,75, 0,198, 0x80, 0x82, 0,37, 0x81, 0,13, 0x90,48, 0x91,72, 0x92,56, 0,236, 
0x81, 0,13, 0x91,77, 0,236, 0x81, 0,13, 0x91,75, 0,236, 0x81, 0,13, 0x91,79, 0,198, 
0x80, 0x82, 0,37, 0x81, 0,13, 0x90,48, 0x91,67, 0x92,55, 0,236, 0x81, 0,13, 0x91,72, 0,236, 
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
// This score contains 1444 bytes, and 4 tone generators are used.
