farvardin/garvuino/arduino_sketches/beeper/arduino_phaser1/g_fight_night.h

const unsigned char music_data[] PROGMEM ={
0x7a,0x8c,0x10,0x00,0x01,0x01,0x00,0xc8,0x01,0x02,0x00,0x28,0x02,0x04,0x00,0x5a,
0x01,0x01,0x00,0x00,0xe0,0x9c,0x1a,0x9d,0x76,0x9d,0xbe,0x9d,0xf9,0x9d,0x34,0x9e,
0xf9,0x9d,0x69,0x9e,0xe0,0x9c,0x1a,0x9d,0x76,0x9d,0xbe,0x9d,0xf9,0x9d,0x34,0x9e,
0xf9,0x9d,0x40,0x9f,0xde,0x9f,0x12,0xa0,0x48,0xa0,0xa8,0x9e,0xc7,0x9e,0xa8,0x9e,
0xc7,0x9e,0xe6,0x9e,0x15,0x9f,0xa8,0x9e,0xc7,0x9e,0x83,0x9f,0xb4,0x9f,0xa8,0x9e,
0xc7,0x9e,0xa8,0x9e,0xc7,0x9e,0xe6,0x9e,0x15,0x9f,0xa8,0x9e,0xc7,0x9e,0x83,0x9f,
0xb4,0x9f,0xba,0xa0,0xf4,0xa0,0xba,0xa1,0xba,0xa0,0x37,0xa1,0xba,0xa0,0xf4,0xa0,
0xba,0xa0,0x7a,0xa1,0xf2,0xa1,0x7b,0xa0,0x05,0xa2,0x18,0xa2,0xf2,0xa1,0x7b,0xa0,
0x05,0xa2,0x18,0xa2,0x91,0xa0,0xa4,0xa0,0x32,0xa2,0x45,0xa2,0xa8,0x9e,0xc7,0x9e,
0xa8,0x9e,0xc7,0x9e,0xe6,0x9e,0x15,0x9f,0xa8,0x9e,0xc7,0x9e,0x83,0x9f,0xb4,0x9f,
0xbd,0x00,0xc9,0x95,0x76,0x01,0x95,0x9c,0x02,0x89,0x95,0x7d,0x01,0x95,0x9c,0x02,
0x89,0x9f,0x76,0x01,0x95,0x9d,0x02,0x89,0x9c,0x7d,0x01,0x95,0x9a,0x02,0x89,0x76,
0x01,0x95,0x98,0x02,0x89,0x98,0x7d,0x01,0x95,0x97,0x02,0x89,0x98,0x76,0x01,0x95,
0x9a,0x7d,0x02,0x89,0x93,0x76,0xbe,0x7d,0x01,0x00,0xbd,0x02,0xc9,0x95,0x76,0xa8,
0xa1,0x01,0x95,0x9c,0x01,0xa8,0xa8,0x01,0x89,0x95,0x7d,0xa6,0xad,0x01,0x95,0x9c,
0x01,0xa6,0xa8,0x01,0x89,0x9f,0x76,0xa1,0xa8,0x01,0x95,0x9d,0x01,0xa1,0x01,0x89,
0x9c,0x7d,0xbe,0xa8,0x01,0x95,0x9a,0x01,0xbe,0xb2,0x01,0x89,0x9a,0x76,0xbe,0xa6,
0x01,0x95,0x98,0x01,0xbe,0xb0,0x01,0x89,0x98,0x7d,0xbe,0xb0,0x01,0x95,0x97,0x01,
0xad,0xaf,0x01,0x89,0x98,0x76,0xad,0xb0,0x01,0x95,0xaf,0x7d,0xad,0xad,0x02,0x89,
0x93,0x76,0xad,0x7d,0x01,0x00,0xbd,0x02,0xc9,0x89,0x76,0xa8,0x01,0x95,0x95,0x01,
0xa8,0x01,0x89,0x89,0x7d,0xa6,0x01,0x95,0x95,0x01,0xa6,0x01,0x89,0x89,0x76,0xa1,
0x01,0x95,0x95,0x01,0xa1,0x01,0x89,0x89,0x7d,0x01,0x95,0x95,0x02,0x89,0x89,0x76,
0x01,0x95,0x95,0x02,0x89,0x89,0x7d,0x01,0x95,0x95,0x01,0xad,0x01,0x89,0x89,0x76,
0xad,0x01,0x95,0x95,0x7d,0xad,0x02,0x89,0x89,0x76,0xad,0x7d,0x01,0x00,0xbd,0x04,
0xf9,0x89,0x76,0x01,0xbe,0x95,0x02,0xbe,0x89,0x7d,0x01,0xbe,0x95,0x02,0xbe,0x89,
0x76,0x01,0xbe,0x95,0x02,0xbe,0x89,0x7d,0x01,0xbe,0x95,0x02,0xb4,0x89,0x76,0x01,
0xbe,0x95,0x02,0xbe,0x89,0x7d,0x01,0xbe,0x95,0x02,0xbe,0x89,0x76,0x01,0xbe,0x95,
0x7d,0x02,0xbe,0x89,0x76,0xbe,0x7d,0x01,0x00,0xbd,0x04,0xe4,0x89,0x76,0x01,0xbe,
0x95,0x02,0xbe,0x89,0x7d,0x01,0xbe,0x95,0x02,0xbe,0x89,0x76,0x01,0xbe,0x95,0x02,
0xbe,0x89,0x7d,0x01,0xbe,0x95,0x02,0xa8,0x89,0x76,0x01,0xbe,0x95,0x02,0xbe,0x89,
0x7d,0x01,0xbe,0x95,0x02,0xa6,0x89,0x76,0x01,0xbe,0x95,0x7d,0x02,0xbe,0x89,0x76,
0xbe,0x7d,0x01,0x00,0xbd,0x04,0xf7,0x90,0x76,0x01,0xbe,0x95,0x02,0xbe,0x90,0x7d,
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
